evan31-gonzalez/Projet-NDVI-Capteur-environnemental-pour-mesure-de-vegetation/3D/images/boite_v0.3_iso.png

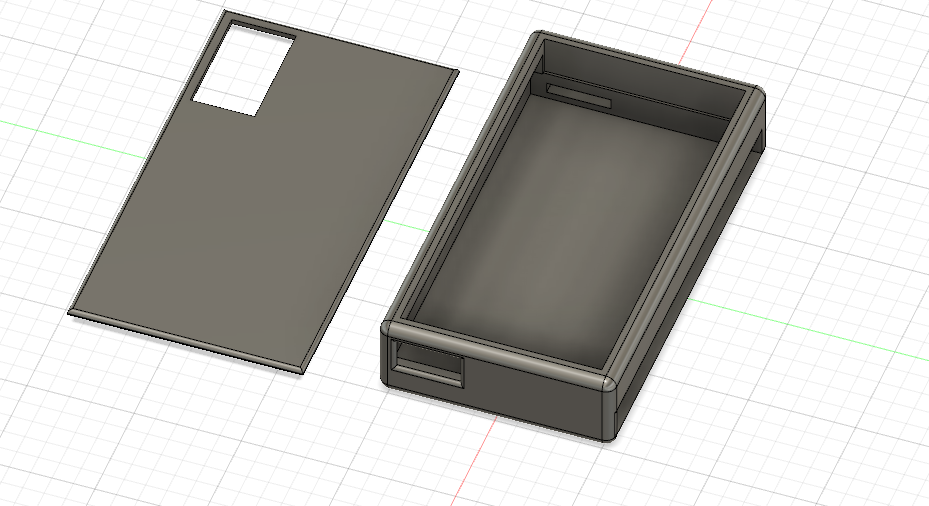
3D/images/boite_v0.3_iso.png
