evan31-gonzalez/Projet-NDVI-Capteur-environnemental-pour-mesure-de-vegetation/pcb/exports/Vue Bottom.png

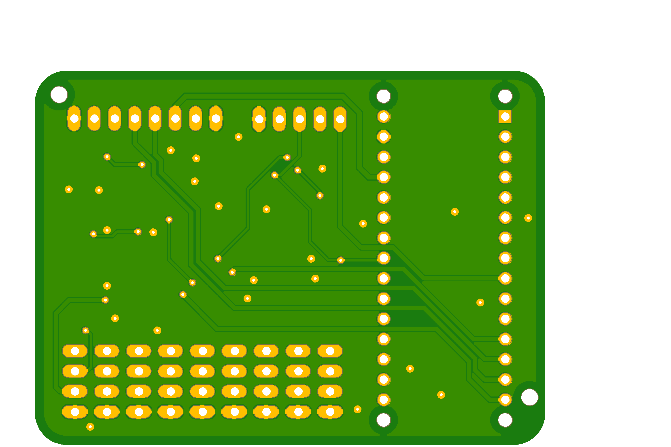
pcb/exports/Vue Bottom.png
