evan31-gonzalez/Projet-NDVI-Capteur-environnemental-pour-mesure-de-vegetation/pcb/exports/Vue Top.png

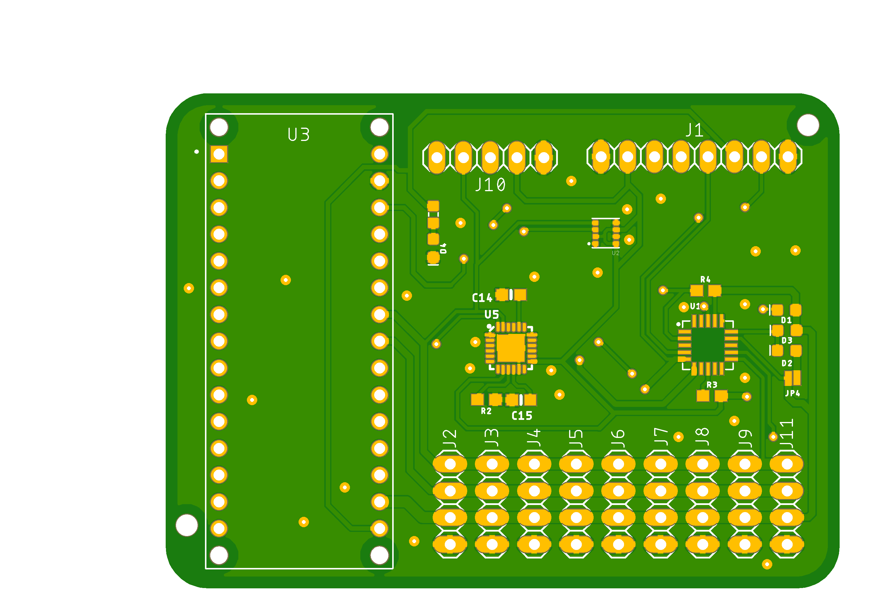
pcb/exports/Vue Top.png
